eurovibes/belegt/spice/probe.asc

C1: cap; 100n
D1: diode; ssa33l
D2: diode; ssa33l
R1: res; 100k
R2: res; 1k
R3: res; 10
R4: res; 20
R5: res; 100000000
U1: PC817B
V1: voltage; 3.3
V2: voltage; SINE(0 15 50)
Named nets: 0
.tran 1s
**********************************
* Copyright:                     *
*   Thomatronik GmbH, Germany    *
*   info@thomatronik.de          *
**********************************
*   PSPICE
.subckt ssa33l 1 2
ddio 1 2 legd
dgr 1 2 grd
.model legd d is = 1.24809E-005 n = 2.3819 rs = 0.0214449
+ eg = 0.4 xti = 0.5 t_measured = 27
+ cjo = 1.19492E-009 vj = 0.700004 m = 0.638376 fc = 0.5
+ tt = 2.4663E-010 bv = 33 ibv = 1 af = 1 kf = 0
.model grd d is = 2.63933E-006 n = 1.01729 rs = 0.022899
+ eg = 0.679652 xti = 0.5 t_measured = 27
.ends
